khkimball/bike-charging-dock/docs/superpowers/plans/2026-09-20-tray-dock.md

# Tray Dock (v2) Implementation Plan

> **For agentic workers:** REQUIRED SUB-SKILL: Use superpowers:subagent-driven-development (recommended) or superpowers:executing-plans to implement this plan task-by-task. Steps use checkbox (`- [ ]`) syntax for tracking.

**Goal:** Replace the v1 cradle deck with a CHRGtime-style flat tray (four bays, cable cutouts, removable dividers), a rounded-corner base holding the charger underneath, and a lift-off lid.

**Architecture:** Same build123d algebra-API project. `tray.py` and `lid.py` are new part modules; `base.py` is reworked for the tray rebate, rounded corners and the tie-down grid; `cradles.py` and `deck.py` are deleted. Tests measure solids. Exports STL + STEP via the existing `scripts/export_all.py` registry.

**Tech Stack:** Python 3.12 via uv, build123d 0.12, pytest. Snapmaker Orca for slicing (see docs/printing.md).

**Spec:** `docs/superpowers/specs/2026-09-20-tray-dock-design.md`

## Global Constraints

- Units mm, Z up, print-bed face at Z=0 for every part.
- WALL 2.4, FLOOR 1.6, TRAY_PLATE 3.0, BAY_DEPTH 32.0, CORNER_R 8.0 (base/lid outer vertical edges).
- CLR_FIT 0.15, CLR_RAIL 0.20, CLR_BAY 3.0 (new), CLR_DEVICE removed.
- BED_X = BED_Y = 250.
- Chamfers not fillets on downward-facing edges; fillets only on vertical edges. No overhang past 45°; bridges ≤ 20 mm allowed.
- Tests measure the built solid; every exported part is one valid solid on the bed (tests/test_parts.py stays).
- `out/` never committed. Every commit message ends with `Co-Authored-By: Claude Fable 5.1 <noreply@anthropic.com>`.
- Coordinates: the tray's plate spans X = 0..TRAY_X, centred on Y = 0; the base wraps it with WALL + CLR_FIT per side; `base.tray_seat()` gives the tray's seating Location; the lid is centred on the base's outer footprint.

## File Structure

```
src/dock/params.py        add CLR_BAY, TRAY_PLATE, BAY_DEPTH, CORNER_R; drop CLR_DEVICE; BED 250x250
src/dock/measurements.py  ROAM/ION/TRACKR all Slab(length, width, thickness); drop Cylinder, port_face, port_height
src/dock/tray.py          layout(), TRAY_X, TRAY_Y, TRAY_H, RAIL_YS, build_tray()
src/dock/base.py          BASE_X/Y/H, REBATE_D, tray_seat(), build_base() with corner fillets and tie grid
src/dock/lid.py           LID_X/Y/H, build_lid()
src/dock/divider.py       unchanged
src/dock/coupon.py        unchanged
scripts/export_all.py     registry: coupon x2, divider, tray, base, lid
tests/test_tray.py, test_base.py, test_lid.py, test_assembly.py, test_parts.py, test_measurements.py, test_params.py
docs/measuring.md, docs/printing.md updated
DELETE src/dock/cradles.py, src/dock/deck.py, tests/test_cradles.py, tests/test_deck.py
```

---

### Task 1: Demolition and parameters

**Files:**
- Modify: `src/dock/params.py`, `src/dock/measurements.py`, `tests/test_params.py`, `tests/test_measurements.py`, `scripts/export_all.py`, `tests/test_parts.py`, `docs/measuring.md`
- Delete: `src/dock/cradles.py`, `src/dock/deck.py`, `tests/test_cradles.py`, `tests/test_deck.py`, `tests/test_assembly.py`, `tests/test_base.py` (base is rebuilt in Task 3; its old tests go with the old base — Task 3 writes new ones), `src/dock/base.py`

**Interfaces:**
- Produces: `params.CLR_BAY = 3.0`, `params.TRAY_PLATE = 3.0`, `params.BAY_DEPTH = 28.0`, `params.CORNER_R = 8.0`, `params.BED_X = params.BED_Y = 250`, `params.CLR_FIT = 0.15`, `params.CLR_RAIL = 0.20`; `params.plug_cutter` and `params.THRU` stay. `measurements.Slab(length, width, thickness)` only; `ROAM = Slab(96.0, 53.0, 24.0)`, `ION = Slab(102.5, 34.7, 30.2)` (lying flat: 34.7 wide, 30.2 tall), `TRACKR = Slab(89.9, 37.1, 29.1)`; `CHARGER` unchanged. `scripts/export_all.py` registers only coupon plate/peg and the divider (sized `height=params.BAY_DEPTH, width=40.0 - params.CLR_RAIL` as a placeholder that Task 2 replaces with tray-derived values).

- [ ] **Step 1: Update tests first.** In `tests/test_params.py` change the design-rule test to assert `CLR_FIT == 0.15`, `CLR_RAIL == 0.20`, `CLR_BAY == 3.0`, `TRAY_PLATE == 3.0`, `BAY_DEPTH == 32.0`, `CORNER_R == 8.0`, `(BED_X, BED_Y) == (250, 250)`, and that `params` has no attribute `CLR_DEVICE`. In `tests/test_measurements.py` keep the positivity test (no `port_offset` special case needed any more), keep the charger envelope, and add `test_devices_are_slabs_with_published_sizes`: `ROAM == Slab(96.0, 53.0, 24.0)`, `ION.width == 34.7 and ION.thickness == 30.2`, `TRACKR.length == 89.9`.
- [ ] **Step 2: Run** `uv run pytest tests/test_params.py tests/test_measurements.py -q` → fails.
- [ ] **Step 3: Edit params.py**: remove `CLR_DEVICE`; set `CLR_FIT = 0.15`, `CLR_RAIL = 0.20`; add

```python
CLR_BAY = 3.0      # device to bay wall, per side (bays, not pockets)
TRAY_PLATE = 3.0   # tray floor thickness (cable cutouts pass through it)
BAY_DEPTH = 32.0   # bay wall height above the tray plate (>= tallest device + 1)
CORNER_R = 8.0     # fillet on the base/lid outer vertical edges
BED_X = 250
BED_Y = 250
```
  and update the module docstring. Keep `Plug`, the three plug envelopes, `plug_cutter`, `THRU`.
- [ ] **Step 4: Edit measurements.py**: delete `Cylinder`, the `port_face`/`port_height` fields and `port_center_height`; `Slab(length, width, thickness)` with a docstring "device lying face-up in a bay: length along the bay, width across it, thickness = height above the bay floor"; set the three devices as above with `# PUBLISHED` comments and the source note; keep `Charger`.
- [ ] **Step 5: Delete** the six v1 files listed above with `git rm`. Rewrite `scripts/export_all.py` so `PARTS` contains `coupon_plate`, `coupon_peg`, `divider` only (placeholder divider size noted in a comment). Ensure `tests/test_parts.py` still imports `PARTS` and passes.
- [ ] **Step 6: docs/measuring.md**: rewrite the three device sections for flat-lying devices (length along the bay, width, thickness; note the published values now in the file; the charger section unchanged). Remove port-height instructions.
- [ ] **Step 7: Run** `uv run pytest -q` → all green (params, measurements, coupon, divider, parts).
- [ ] **Step 8: Commit** `"v2: remove cradle deck, add tray parameters and flat device measurements"`.

---

### Task 2: Tray

**Files:**
- Create: `src/dock/tray.py`, `tests/test_tray.py`
- Modify: `scripts/export_all.py`

**Interfaces:**
- Consumes: `params.WALL, TRAY_PLATE, BAY_DEPTH, CLR_BAY, CLR_RAIL, CORNER_R, CLR_FIT, BED_X, BED_Y, USB_A_PLUG`; `measurements.ROAM, ION, TRACKR`; `divider.RAIL_D, RAIL_W, rail_cutter(height)`.
- Produces:
  - `tray.CUTOUT = (22.0, 12.0)` cable cutout size (along the bay, across the bay).
  - `tray.ROAM_BAY = (x0, y0, w, l)` and `tray.RIGHT_BAYS = {"ion": (...), "trackr": (...), "spare": (...)}` bay interiors as (min X, min Y, X size, Y size) in tray coordinates.
  - `tray.TRAY_X, tray.TRAY_Y` outer plate size; `tray.TRAY_H = TRAY_PLATE + BAY_DEPTH`; `tray.OUTER_R = CORNER_R - WALL - CLR_FIT` corner radius of the tray outline.
  - `tray.RAIL_YS: tuple[float, float]` Y centres of the two removable dividers; `tray.RIGHT_BAY_W` (X size of the right bays, = divider width + CLR_RAIL).
  - `build_tray() -> Part`.

Layout (tray coordinates, X = 0..TRAY_X, Y centred on 0):
- Left bay interior: X size = ROAM.width + 2·CLR_BAY (59), Y size = ROAM.length + 2·CLR_BAY + CUTOUT[0] (= 96 + 6 + 22 = 124). Cutout at the −Y end, centred in X.
- Right column interior X size = max over devices of (length + 2·CLR_BAY) + CUTOUT[0] (Ion: 102.5 + 6 + 22 = 130.5). Three bays stacked in Y: heights ION.width + 2·CLR_BAY (40.7), TRACKR.width + 2·CLR_BAY (43.1), spare = 40.0; separated by the two removable dividers (divider THICK = 2.0 counts in the stack). Cutouts at the +X end of each bay, centred in the bay's Y.
- Right column total Y = 40.7 + 2 + 43.1 + 2 + 40 = 127.8; the left bay is stretched to the same Y (its cutout stays at the −Y end).
- Fixed walls: four outer + one partition between the left bay and the right column. TRAY_X = 3·WALL + 59 + 130.5 = 196.7; TRAY_Y = 2·WALL + 127.8 = 132.6.
- Rail slots for the two dividers: cut with `divider.rail_cutter(BAY_DEPTH)` wholly inside the partition wall (its +X face) and the +X outer wall (its −X face), at the two `RAIL_YS`; to keep ≥ WALL behind the slot, the partition wall is `WALL + RAIL_D + CLR_RAIL` thick and the +X outer wall likewise (adjust TRAY_X accordingly and expose the real number).
- Outer vertical corners of the tray filleted `OUTER_R`; plate bottom outer edge chamfered 1.0 (downward edge); bay inner corners square.
- Cable cutouts: `Box(CUTOUT[0], CUTOUT[1], THRU)` through the plate only (they must not cut walls), positioned 2 mm in from the bay's end wall.

- [ ] **Step 1: Failing tests** `tests/test_tray.py`:

```python
from build123d import Axis
from dock import tray, params, divider
from dock import measurements as m

def test_tray_fits_bed():
    s = tray.build_tray().bounding_box().size
    assert s.X <= params.BED_X and s.Y <= params.BED_Y

def test_tray_is_one_valid_solid_on_bed():
    p = tray.build_tray()
    assert p.is_valid and len(p.solids()) == 1
    assert abs(p.bounding_box().min.Z) < 1e-6
    assert abs(p.bounding_box().size.Z - tray.TRAY_H) < 1e-6

def test_four_cable_cutouts_through_the_plate():
    p = tray.build_tray()
    bottom = p.faces().sort_by(Axis.Z)[0]
    wires = bottom.inner_wires()
    assert len(wires) == 4
    for w in wires:
        s = w.bounding_box().size
        assert {round(s.X, 3), round(s.Y, 3)} == {tray.CUTOUT[0], tray.CUTOUT[1]}

def test_each_device_fits_its_bay_with_clearance():
    for dev, (x0, y0, w, l) in ((m.ROAM, tray.ROAM_BAY),):
        assert w >= dev.width + 2 * params.CLR_BAY - 1e-6
        assert l >= dev.length + 2 * params.CLR_BAY + tray.CUTOUT[0] - 1e-6
    for name, dev in (("ion", m.ION), ("trackr", m.TRACKR)):
        x0, y0, w, l = tray.RIGHT_BAYS[name]
        assert w >= dev.length + 2 * params.CLR_BAY + tray.CUTOUT[0] - 1e-6
        assert l >= dev.width + 2 * params.CLR_BAY - 1e-6

def test_bays_are_open_voids_of_full_depth():
    """A box the size of each bay interior, sitting on the plate, does not intersect the tray."""
    from build123d import Box, Pos, Align
    p = tray.build_tray()
    bays = [tray.ROAM_BAY, *tray.RIGHT_BAYS.values()]
    for (x0, y0, w, l) in bays:
        probe = Pos(x0 + w / 2, y0 + l / 2, params.TRAY_PLATE) * Box(w - 0.01, l - 0.01, params.BAY_DEPTH - 0.01, align=(Align.CENTER, Align.CENTER, Align.MIN))
        assert (probe & p).volume < 1e-3

def test_divider_drops_into_both_rail_positions():
    from build123d import Pos
    p = tray.build_tray()
    d = divider.build_divider(height=params.BAY_DEPTH, width=tray.RIGHT_BAY_W - params.CLR_RAIL)
    for y in tray.RAIL_YS:
        placed = Pos(tray.RIGHT_BAYS["ion"][0] + tray.RIGHT_BAY_W / 2, y, params.TRAY_PLATE) * d
        assert (placed & p).volume < 1e-3

def test_walls_keep_full_thickness_behind_rail_slots():
    """Probe the material behind each rail slot: at least WALL remains."""
    from build123d import Box, Pos, Align
    p = tray.build_tray()
    x_part = tray.RIGHT_BAYS["ion"][0]          # partition's +X face
    for y in tray.RAIL_YS:
        probe = Pos(x_part - divider.RAIL_D - params.CLR_RAIL - params.WALL / 2, y, params.TRAY_PLATE + 1) * Box(params.WALL - 0.02, 2, params.BAY_DEPTH - 2, align=(Align.CENTER, Align.CENTER, Align.MIN))
        assert abs((probe & p).volume - probe.volume) < 1e-3

def test_outer_corners_are_rounded():
    from build123d import GeomType
    p = tray.build_tray()
    cyl = [f for f in p.faces() if f.geom_type == GeomType.CYLINDER and abs(f.radius - tray.OUTER_R) < 1e-6]
    assert len(cyl) >= 4

def test_no_overhang_past_45_degrees():
    import math
    p = tray.build_tray()
    for f in p.faces():
        n = f.normal_at()
        if n.Z < -1e-6 and f.center().Z > 1e-6:
            angle = math.degrees(math.acos(-n.Z))   # 0 = flat ceiling
            assert angle >= 45 - 1e-6 or f.bounding_box().size.length <= 20, f.center()
```

- [ ] **Step 2: Run** → ModuleNotFoundError.
- [ ] **Step 3: Implement `src/dock/tray.py`** per the layout above. Build order: plate (rounded outline via `fillet` on the plate's vertical edges, or build the outline as a rounded rectangle sketch and extrude), add outer walls and partition as boxes fused on top, cut the four cutouts through the plate with `Box(..., THRU)` positioned so they cannot touch walls, cut the rail slots, chamfer the bottom outer edge. Expose all interface constants at module level computed from params/measurements/divider.
- [ ] **Step 4: Iterate to green.** Register `"tray": tray.build_tray` and change the divider export to `lambda: divider.build_divider(height=params.BAY_DEPTH, width=tray.RIGHT_BAY_W - params.CLR_RAIL)`.
- [ ] **Step 5: Commit** `"Add flat tray with four bays, cable cutouts and divider rails"`.

---

### Task 3: Base rework

**Files:**
- Create: `src/dock/base.py` (fresh), `tests/test_base.py` (fresh)
- Modify: `scripts/export_all.py`

**Interfaces:**
- Consumes: `tray.TRAY_X, TRAY_Y, TRAY_H, OUTER_R`; `measurements.CHARGER`; `params.*`.
- Produces: `base.BASE_X = TRAY_X + 2·(WALL + CLR_FIT)`, `base.BASE_Y = TRAY_Y + 2·(WALL + CLR_FIT)`, `base.REBATE_D = TRAY_H`, `base.CABLE_ROOM = 15.0`, `base.BASE_H = FLOOR + CHARGER.height + CABLE_ROOM + REBATE_D`, `base.tray_seat() -> Location` (= `Pos(WALL + CLR_FIT, 0, BASE_H - REBATE_D)`), `base.CAVITY_*`, `base.FENCE_CX`, `base.TIE_GRID` (list of hole centres), `build_base() -> Part`.

Geometry:
- Outer box `BASE_X × BASE_Y × BASE_H` from X = 0, centred in Y, vertical edges filleted `CORNER_R`. Lower cavity: walls `2·WALL` thick, floor `FLOOR`, inner vertical corners filleted `CORNER_R − 2·WALL` (so the fillet tool succeeds; if it fails, leave square and say so). Rebate on top, `REBATE_D` deep, `TRAY_X + 2·CLR_FIT` by `TRAY_Y + 2·CLR_FIT`, with the tray's corner radius + CLR_FIT; the ledge is `WALL − CLR_FIT` wide.
- Charger fence (revised 2026-09-21 after the manual): the charger's back is against the −X cavity wall with `POCKET_BACK_SLACK` 2 mm; the fence is a U (±Y sides and +X front, no back wall); the cord port in the −X wall lines up with the inlet so the C7 end plugs in from outside; ports face +X with the rest of the cavity in front; the cable loop row is 24 mm in front of the fence and the tie grid (24 mm pitch) fills the floor from there to the +X wall. `PORT_PLUG_ROOM_MIN = 40` is an assertion only.
- Cord port (ruling after review): a closed hole in the −X end wall, 20 wide × 16 tall, bottom at FLOOR + 2, centred on Y = 0, entirely below the rebate ledge; rim and ledge stay continuous. BASE_Y = max(tray-driven, fence-driven + 2 mm per side). Base bottom outer edge chamfered CHAMFER.
- Escape port: rear (−Y) wall, `USB_A_PLUG.width + 4` wide × 12 tall, top one WALL below the rebate ledge, centred on the spare bay's X (use `tray.RIGHT_BAYS["spare"]`).
- LED window: +X end wall, 4 × 4, centred at `FLOOR + CHARGER.height/2`, Y = `POCKET_MIN_Y + port_face_margin − led_offset_from_ports` (outboard of port 1).
- Tie-down grid: 4 mm through-holes on a 12 mm pitch in the floor, covering the free floor between the fence's +X wall + 6 mm and the +X cavity wall − 6 mm, full cavity Y minus 6 mm margins. Chamfer 0.6 on their bottom (bed) edges is optional; skip if fussy.
- Foot recesses: four Ø10 × 0.6 under the corners, 12 mm in.
- Rear cutters sized `2·WALL + 0.5` from the outer face.

- [ ] **Step 1: Failing tests** `tests/test_base.py` — all measured on the solid: outer size = tray + 2·(WALL+CLR_FIT) in X (Y may be larger, assert ≥); valid single solid on bed; rebate opening (measured on the ledge face, aggregating faces) = TRAY + 2·CLR_FIT in X and Y; four foot recesses on the bed face; the fence's outer bbox lies inside the cavity with ≥ 2 mm Y margin; ≥ 40 mm free X in front of the port face; cord port is a closed through-hole in the −X wall below the ledge, centred on Y=0; rim and ledge continuous all round; LED window centre inside the pocket's Y span and outboard of port 1; escape port hole present in the rear wall below the ledge; tie grid holes: count on the bed face equals `len(TIE_GRID) + 4`; outer vertical corners rounded at `CORNER_R` (≥ 4 cylindrical faces); overhang test allowlisting bridges ≤ 20 mm.
- [ ] **Step 2: Run** → fails. **Step 3: Implement.** **Step 4: Iterate to green**, register `"base": base.build_base`. **Step 5: Commit** `"Rebuild base for the tray: rounded corners, rebate, tie-down grid"`.

---

### Task 4: Lid

**Files:**
- Create: `src/dock/lid.py`, `tests/test_lid.py`
- Modify: `scripts/export_all.py`

**Interfaces:**
- Consumes: `base.BASE_X, BASE_Y`, `params.WALL, CLR_FIT, CORNER_R, CHAMFER`.
- Produces: `lid.SKIRT_H = 8.0`, `lid.LID_X = BASE_X + 2·(WALL + CLR_FIT)`, `lid.LID_Y = ...`, `lid.LID_H = WALL + SKIRT_H`, `lid.OUTER_R = CORNER_R + WALL + CLR_FIT`, `build_lid() -> Part` built top-face-down (top plate on the bed at Z = 0, skirt rising to Z = LID_H), and `lid.lid_seat() -> Location` that flips and places it on the base (top at `BASE_H + WALL`, skirt overlapping the base's top `SKIRT_H`).

- [ ] **Step 1: Failing tests** `tests/test_lid.py`: single valid solid on bed; bbox = LID_X × LID_Y × LID_H; the skirt's inner opening (measured on the top face at Z = LID_H, inner wire) = BASE_X + 2·CLR_FIT by BASE_Y + 2·CLR_FIT; outer corners rounded at `OUTER_R`; no downward faces except the bed face (prints with zero overhang); top outer edge chamfered (the chamfer sits on the bed side when printing: assert ≥ 1 planar face at 45°).
- [ ] **Step 2–4:** implement, iterate, register `"lid": lid.build_lid`.
- [ ] **Step 5: Commit** `"Add lift-off lid"`.

---

### Task 5: Assembly, docs, handoff

**Files:**
- Create: `tests/test_assembly.py`
- Modify: `docs/printing.md`, `README.md`, `CLAUDE.md` (conventions mention tray/lid, drop cradles)

- [ ] **Step 1: Tests** `tests/test_assembly.py`:
  - tray seated via `base.tray_seat()` does not intersect the base (volume < 1e-3) and its bay-wall tops are flush with the base rim (measure the tray's top Z after seating vs `base.BASE_H`);
  - lid seated via `lid.lid_seat()` does not intersect the base or the seated tray;
  - a device-sized box (each of ROAM, ION, TRACKR at its bay position on the seated tray's plate) does not intersect the seated lid (i.e. the lid clears the tallest device: assert `BAY_DEPTH >= max thickness` too);
  - dividers at both rail positions on the seated tray do not intersect base or lid;
  - assembled footprint (lid bbox) ≤ BED limits.
- [ ] **Step 2: Run** and fix geometry until green.
- [ ] **Step 3: Docs.** `docs/printing.md`: parts table becomes coupon, divider ×2, tray (plate down, bays up, no supports), base (open top up, no supports; ceilings = escape port, LED window, foot recesses), lid (top face down, no supports). Print order: coupon → dividers + tray → base → lid. Keep the Flatpak/absolute-path notes and `scripts/orca_check.sh`. `README.md` and `CLAUDE.md` updated to name the three parts.
- [ ] **Step 4: Run** `uv run pytest -q` and `uv run python scripts/export_all.py` and `scripts/orca_check.sh`.
- [ ] **Step 5: Commit** `"Assembly tests and v2 printing guide"`.

---

## Self-review

- Spec coverage: base (T3, incl. tie grid, corners, rebate), tray (T2), lid (T4), divider reuse (T2/T5), measurements as slabs (T1), bed limit (T1), removed v1 (T1), docs (T5). Hinge/felt/latch out of scope per spec.
- Placeholders: the divider export size in T1 is an explicit placeholder replaced in T2 (stated).
- Names: `tray.TRAY_X/TRAY_Y/TRAY_H/OUTER_R/RAIL_YS/RIGHT_BAY_W/ROAM_BAY/RIGHT_BAYS/CUTOUT`, `base.BASE_X/BASE_Y/BASE_H/REBATE_D/tray_seat()/TIE_GRID`, `lid.LID_X/LID_Y/LID_H/SKIRT_H/OUTER_R/lid_seat()` used consistently across T2–T5.
